Drachenkaetzchen/TinyMix3/FrontPanel_bot.png

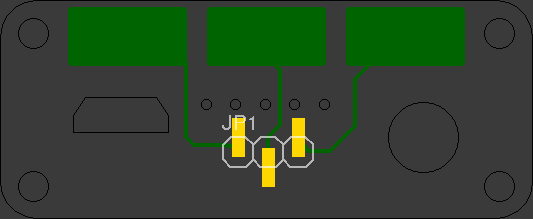
FrontPanel_bot.png
